opennukit/Nukit-Open-Upper-Room-UVGI/LaserCut/Nukit Open Upper Room UVGI Pendent Fixture/Nukit Open Upper Room UVGI Pendent Variants/Nukit Open Upper Room UVGI  Pendent Fixture v1 revision c/Nukit Open Upper Room UVGI  Pendent Fixture v1 revision c 3mm/3rd ring x 1.dxf

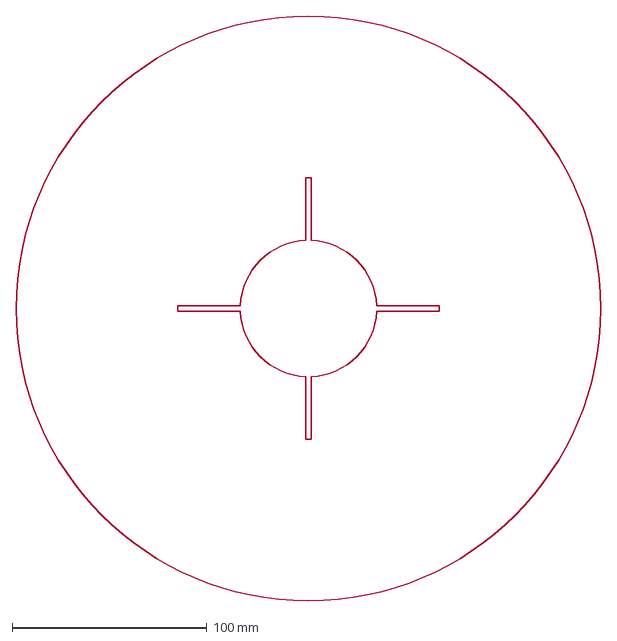
[picture p21: CAD file, 2024-01-10]
LaserCut/Nukit Open Upper Room UVGI Pendent Fixture/Nukit Open Upper Room UVGI Pendent Variants/Nukit Open Upper Room UVGI Pendent Fixture v1 revision c/Nukit Open Upper Room UVGI Pendent Fixture v1 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
300.0 x 300.0 mm
